abierto-cc/fenderino/software/examples/FA_7_escala_con_voz/voz.h

// Liberia Talkie por 2011 Peter Knight
// Usamos una voz femenina con acento americano
// GPLv2

//const uint8_t spTHE[]       PROGMEM = {0x08,0xE8,0x3E,0x55,0x01,0xC3,0x86,0x27,0xAF,0x72,0x0D,0x4D,0x97,0xD5,0xBC,0x64,0x3C,0xF2,0x5C,0x51,0xF1,0x93,0x36,0x8F,0x4F,0x59,0x2A,0x42,0x7A,0x32,0xC3,0x64,0xFF,0x3F};
//const uint8_t spTIME[]      PROGMEM = {0x0E,0x28,0xAC,0x2D,0x01,0x5D,0xB6,0x0D,0x33,0xF3,0x54,0xB3,0x60,0xBA,0x8C,0x54,0x5C,0xCD,0x2D,0xD4,0x32,0x73,0x0F,0x8E,0x34,0x33,0xCB,0x4A,0x25,0xD4,0x25,0x83,0x2C,0x2B,0xD5,0x50,0x97,0x08,0x32,0xEC,0xD4,0xDC,0x4C,0x33,0xC8,0x70,0x73,0x0F,0x33,0xCD,0x20,0xC3,0xCB,0x43,0xDD,0x3C,0xCD,0x8C,0x20,0x77,0x89,0xF4,0x94,0xB2,0xE2,0xE2,0x35,0x22,0x5D,0xD6,0x4A,0x8A,0x96,0xCC,0x36,0x25,0x2D,0xC9,0x9A,0x7B,0xC2,0x18,0x87,0x24,0x4B,0x1C,0xC9,0x50,0x19,0x92,0x2C,0x71,0x34,0x4B,0x45,0x8A,0x8B,0xC4,0x96,0xB6,0x5A,0x29,0x2A,0x92,0x5A,0xCA,0x53,0x96,0x20,0x05,0x09,0xF5,0x92,0x5D,0xBC,0xE8,0x58,0x4A,0xDD,0xAE,0x73,0xBD,0x65,0x4B,0x8D,0x78,0xCA,0x2B,0x4E,0xD8,0xD9,0xED,0x22,0x20,0x06,0x75,0x00,0x00,0x80,0xFF,0x07};
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

/* ejemplo de uso:
 *  
 * voz.say(spGOOD);
 * voz.say(spMORNING);
 * voz.say(spPAUSE1);
 * voz.say(spTHE);
 * voz.say(spTIME);
 * voz.say(spIS);
 * voz.say(spELEVEN);
 * voz.say(spTHIRTY);
 * voz.say(spSIX);
 * voz.say(spA_M_);
 * voz.say(spPAUSE1);
 */
